codesamu/MISS/3D/animation-scene/bin-sorting.png

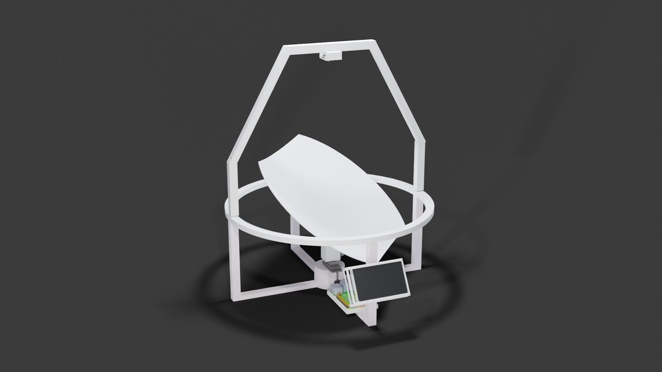
3D/animation-scene/bin-sorting.png
