codesamu/MISS/3D/animation-scene/bin.png

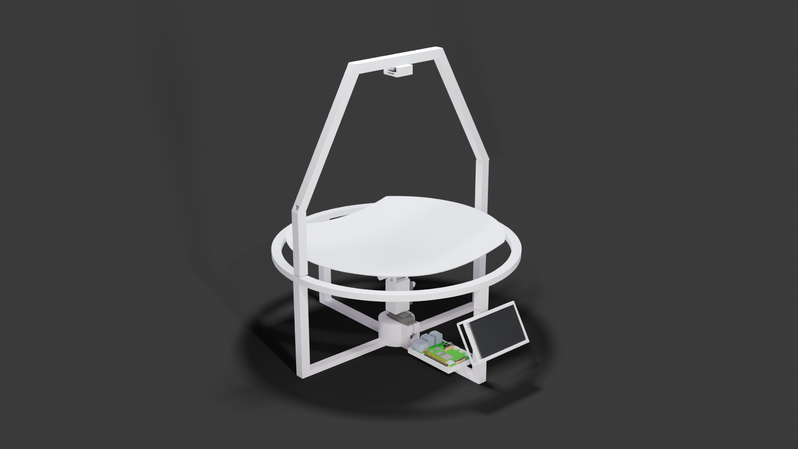
3D/animation-scene/bin.png
