codesamu/MISS/3D/plastic-water-bottle/textures/4715.jpeg

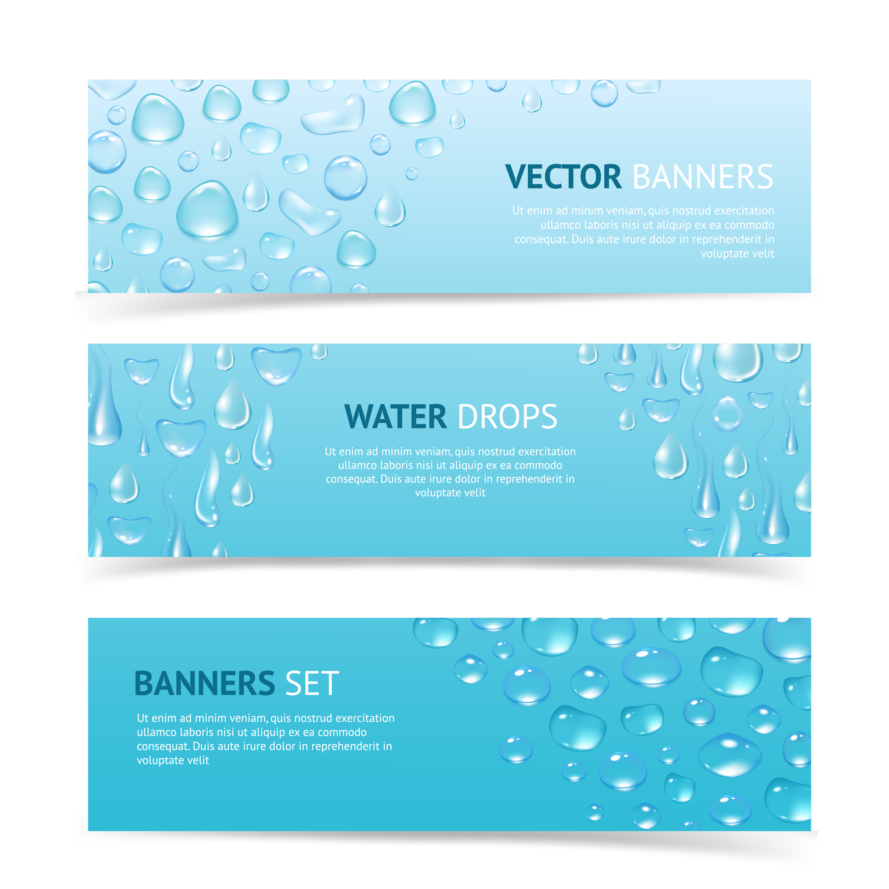
3D/plastic-water-bottle/textures/4715.jpeg
