codesamu/MISS/display-cam-gui/temp_captured.jpg

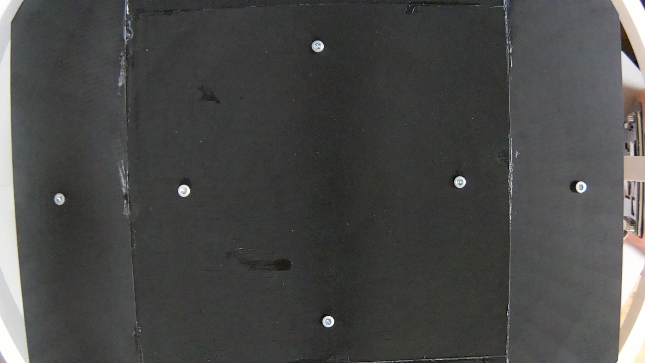
display-cam-gui/temp_captured.jpg
