codesamu/MISS/Doku-IMG/Ablauf-MISS.png

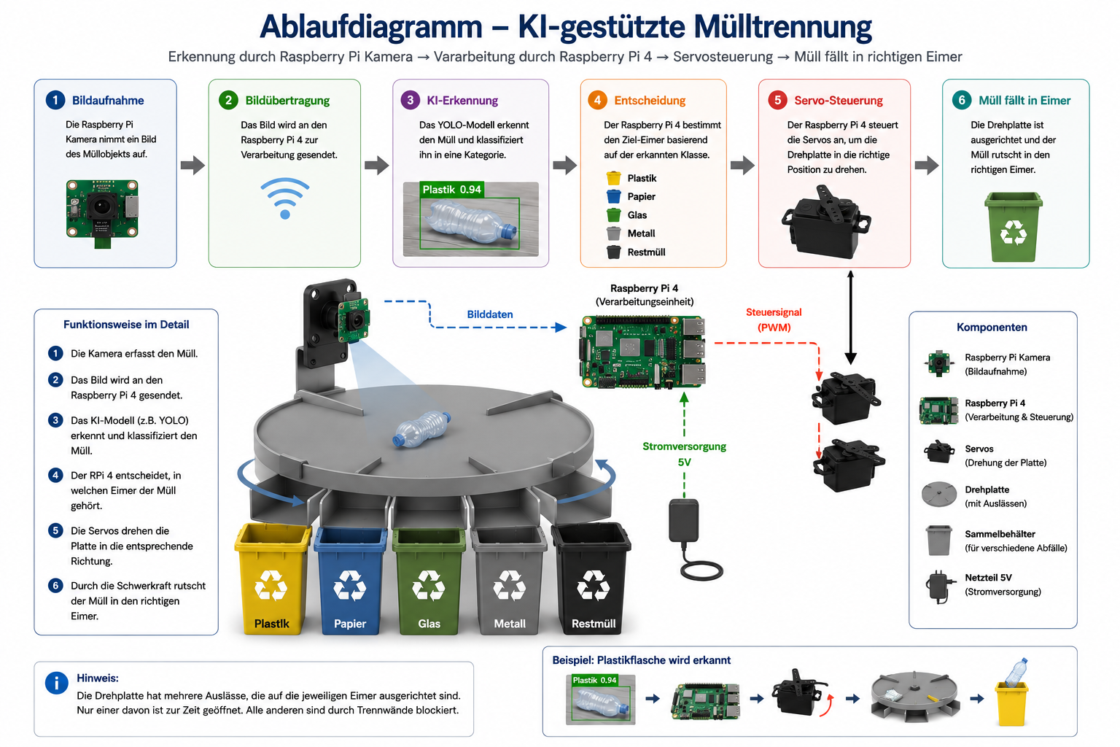
Doku-IMG/Ablauf-MISS.png
