codesamu/MISS/Doku-IMG/AT-Recycle.png

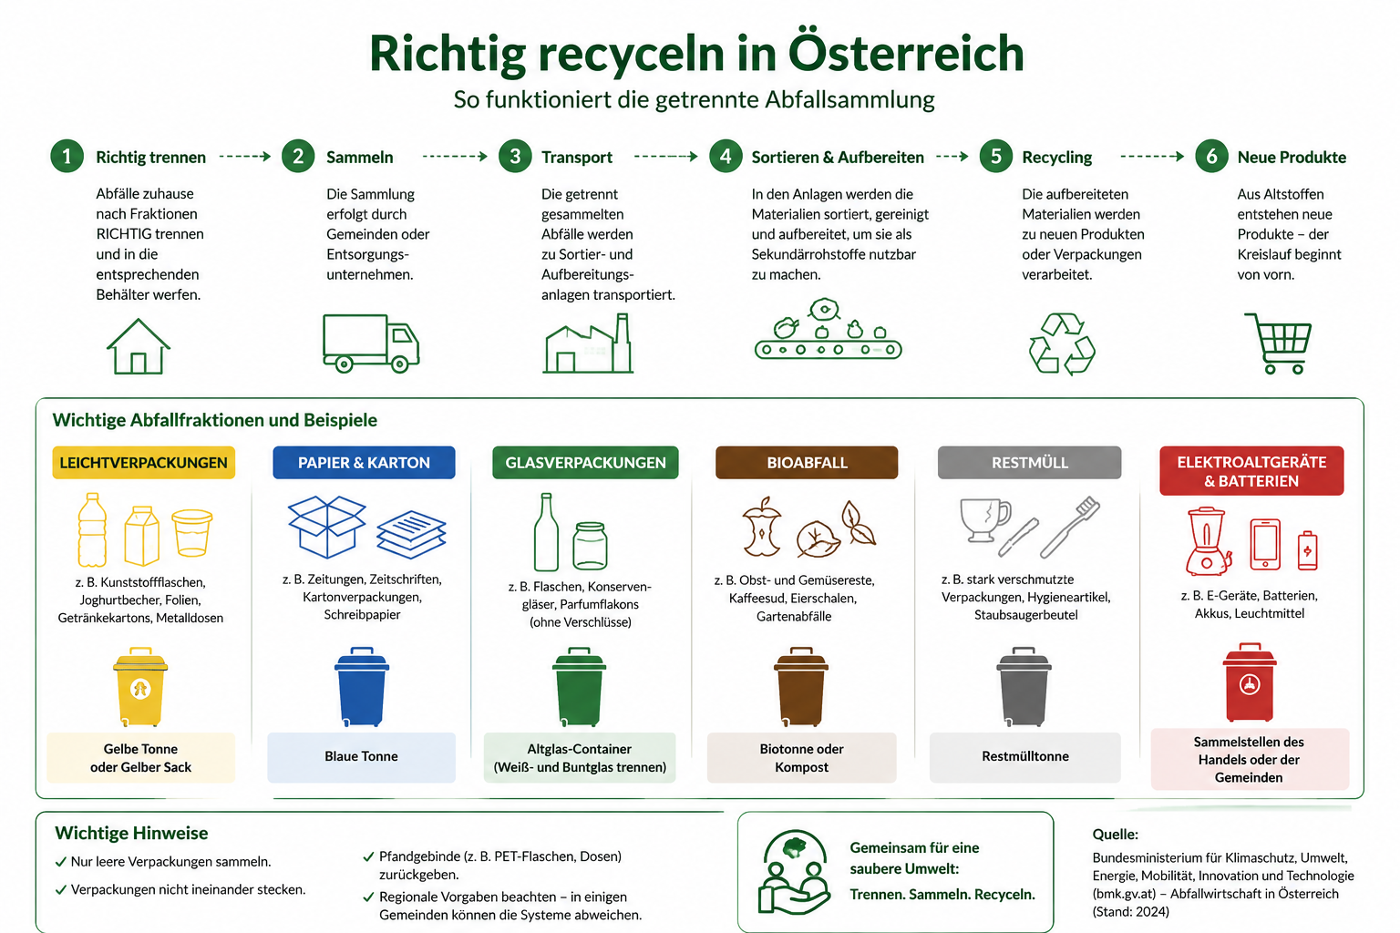
Doku-IMG/AT-Recycle.png
