codesamu/MISS/Doku-IMG/Cam_IMG.png

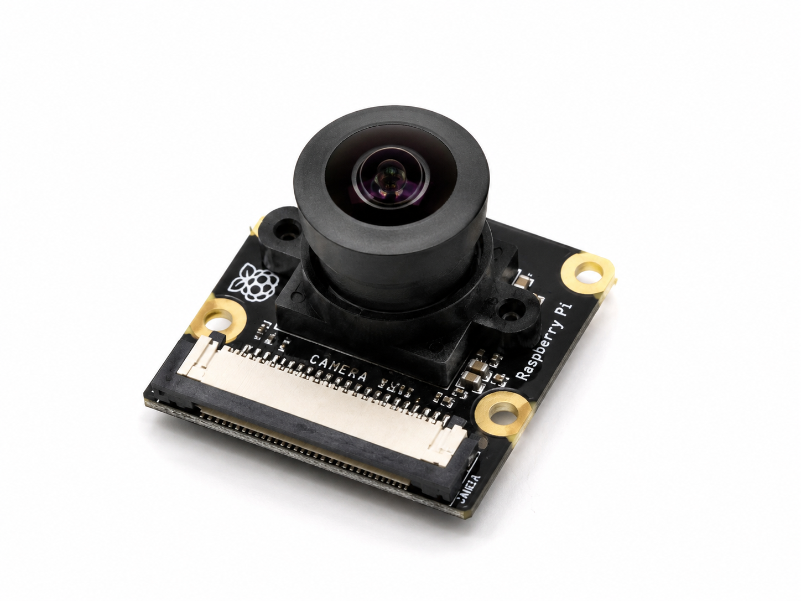
Doku-IMG/Cam_IMG.png
