codesamu/MISS/Doku-IMG/Funktion-YOLO.png

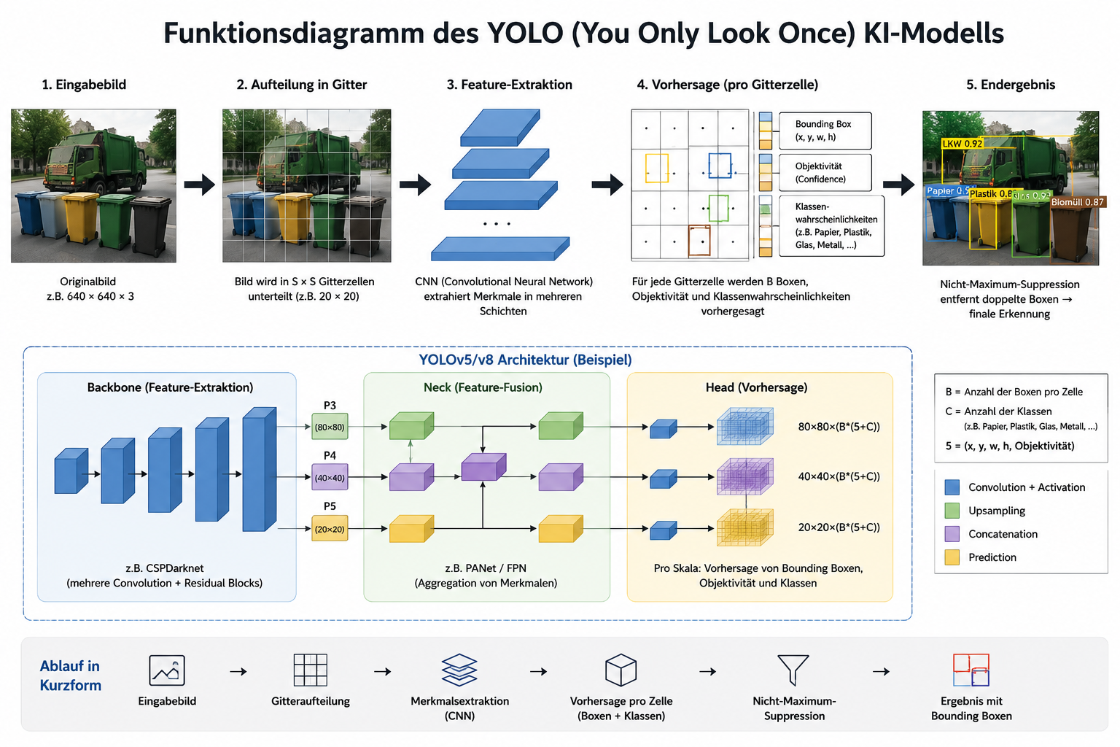
Doku-IMG/Funktion-YOLO.png
