codesamu/MISS/Doku-IMG/Nachhaltigkeit-Trennen.png

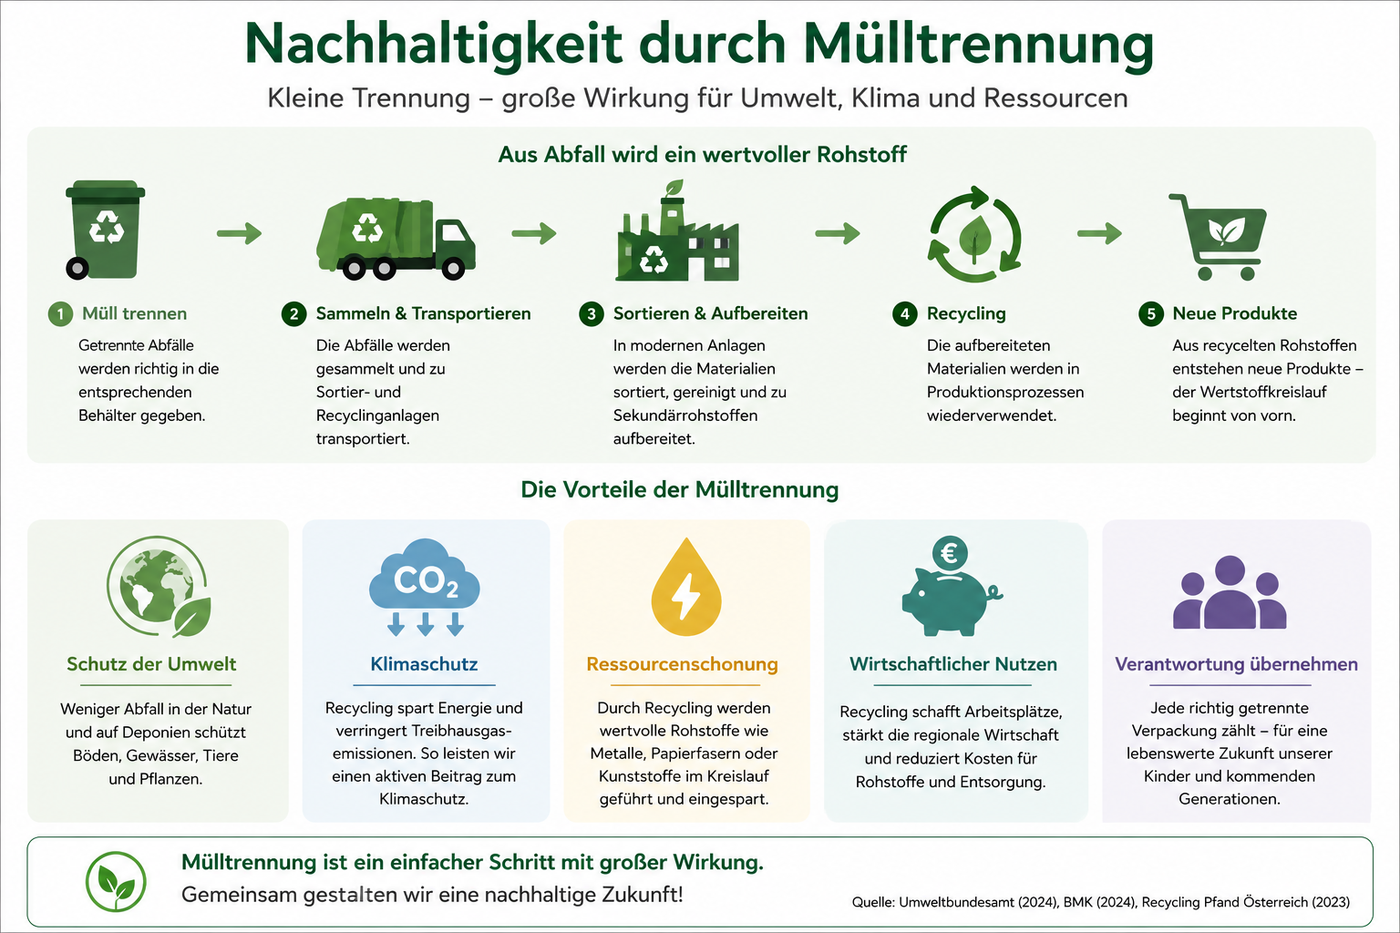
Doku-IMG/Nachhaltigkeit-Trennen.png
