codesamu/MISS/Doku-IMG/RPI_IMG.png

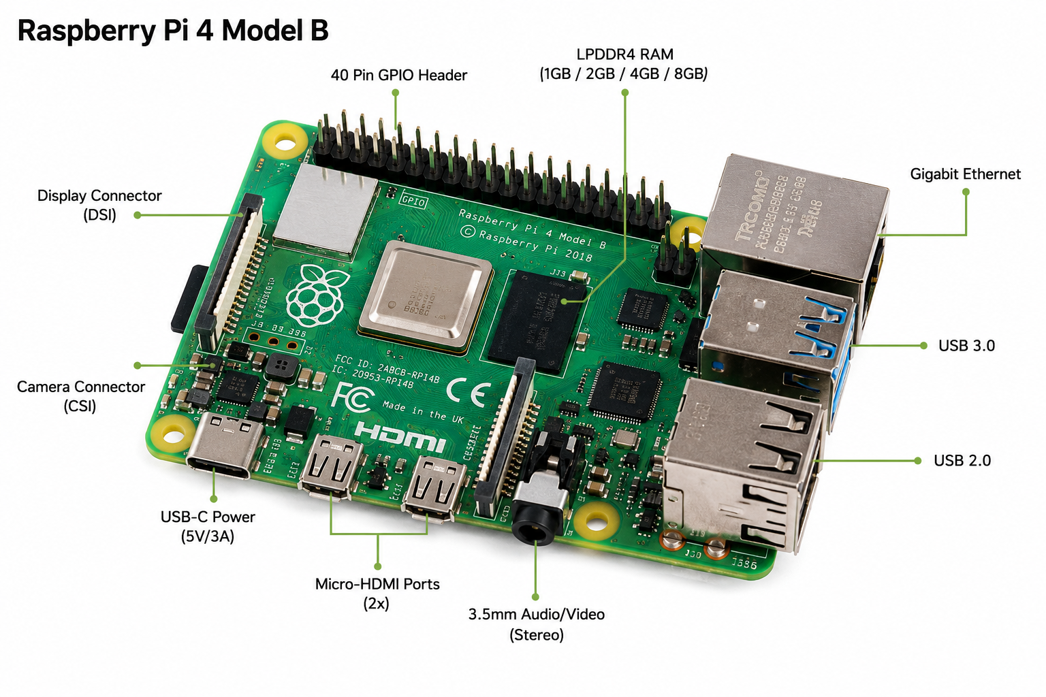
Doku-IMG/RPI_IMG.png
