codesamu/MISS/Doku-IMG/Servo_IMG.png

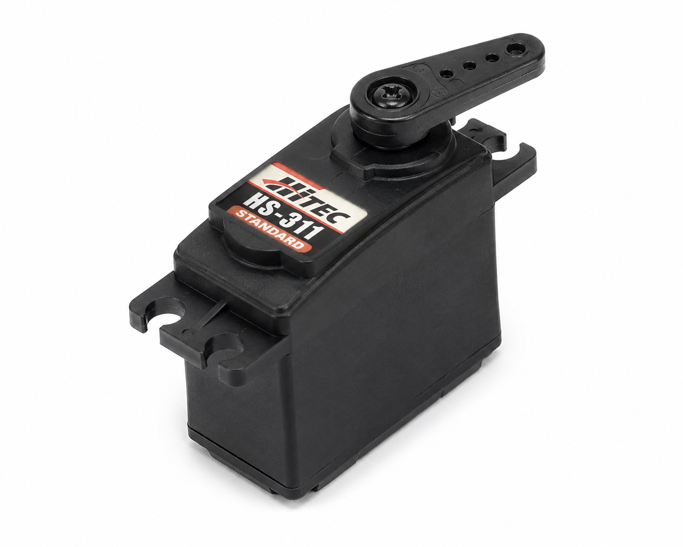
Doku-IMG/Servo_IMG.png
