codesamu/MISS/Doku-IMG/System-Markt.png

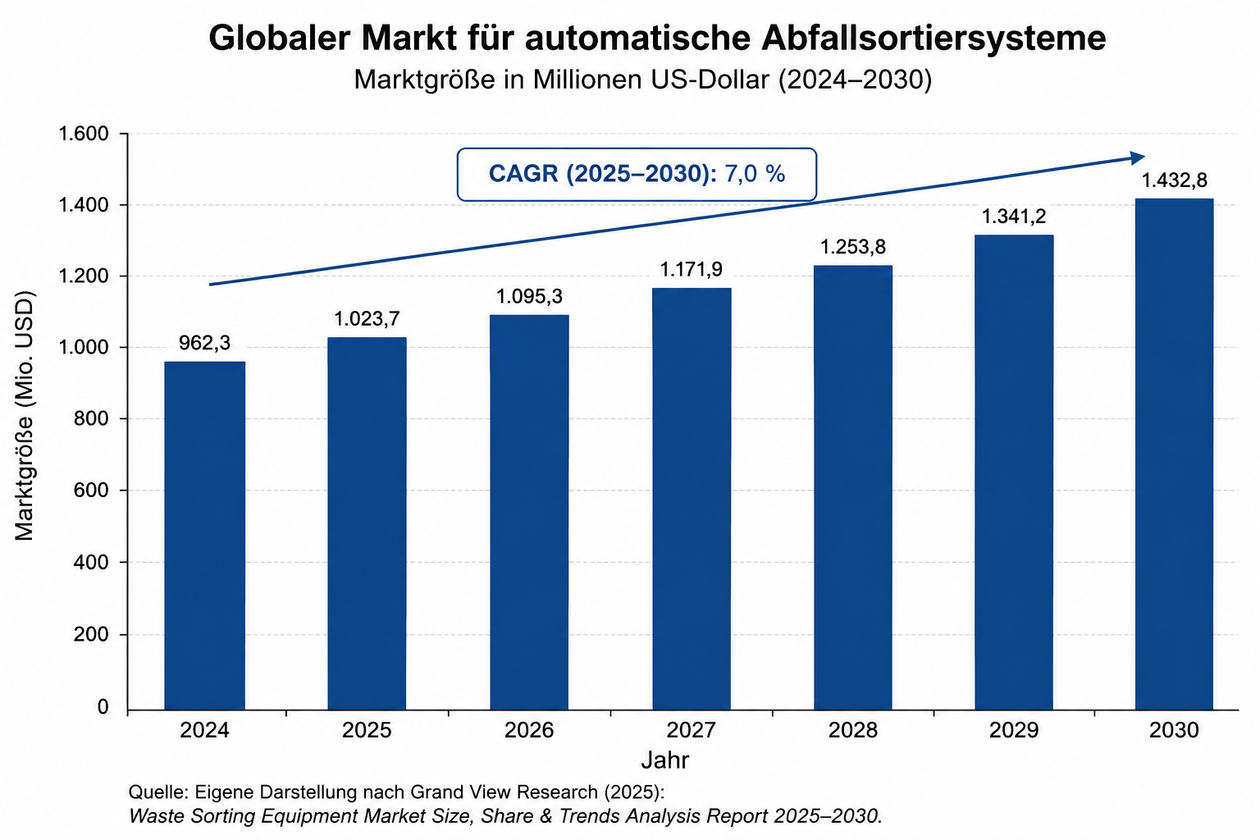
Doku-IMG/System-Markt.png
