codesamu/MISS/YOLO/runs/pet_jhp02naa/train/BoxF1_curve.png

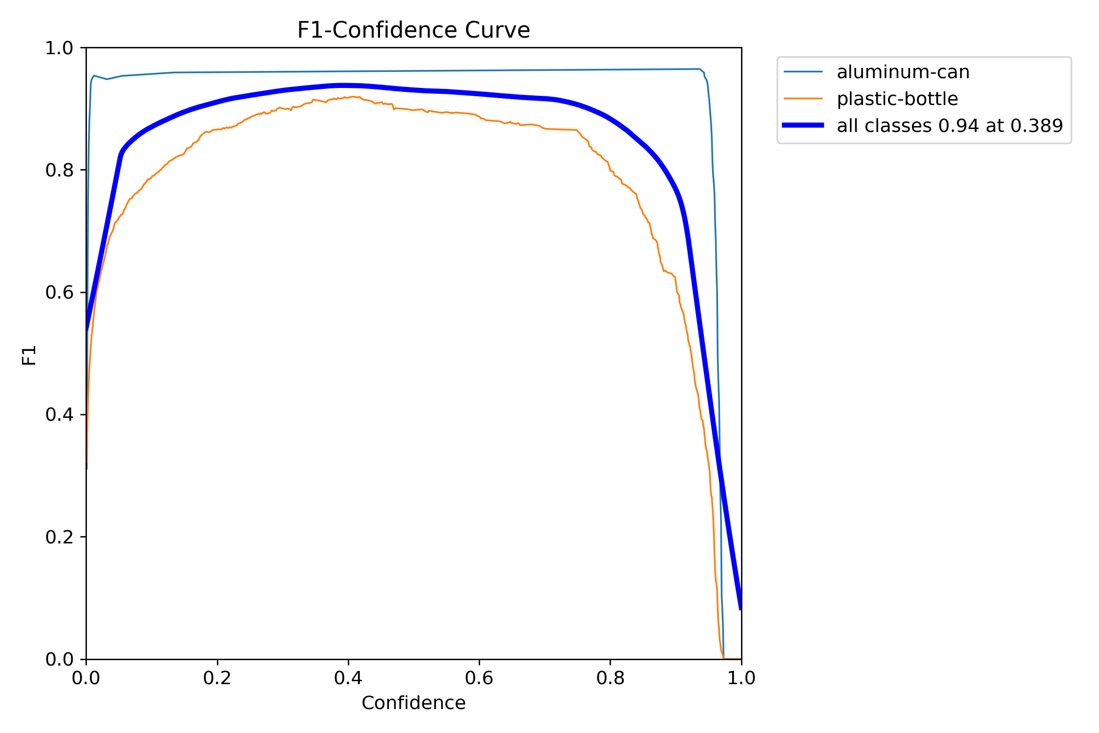
YOLO/runs/pet_jhp02naa/train/BoxF1_curve.png
