codesamu/MISS/YOLO/runs/pet_jhp02naa/train/BoxP_curve.png

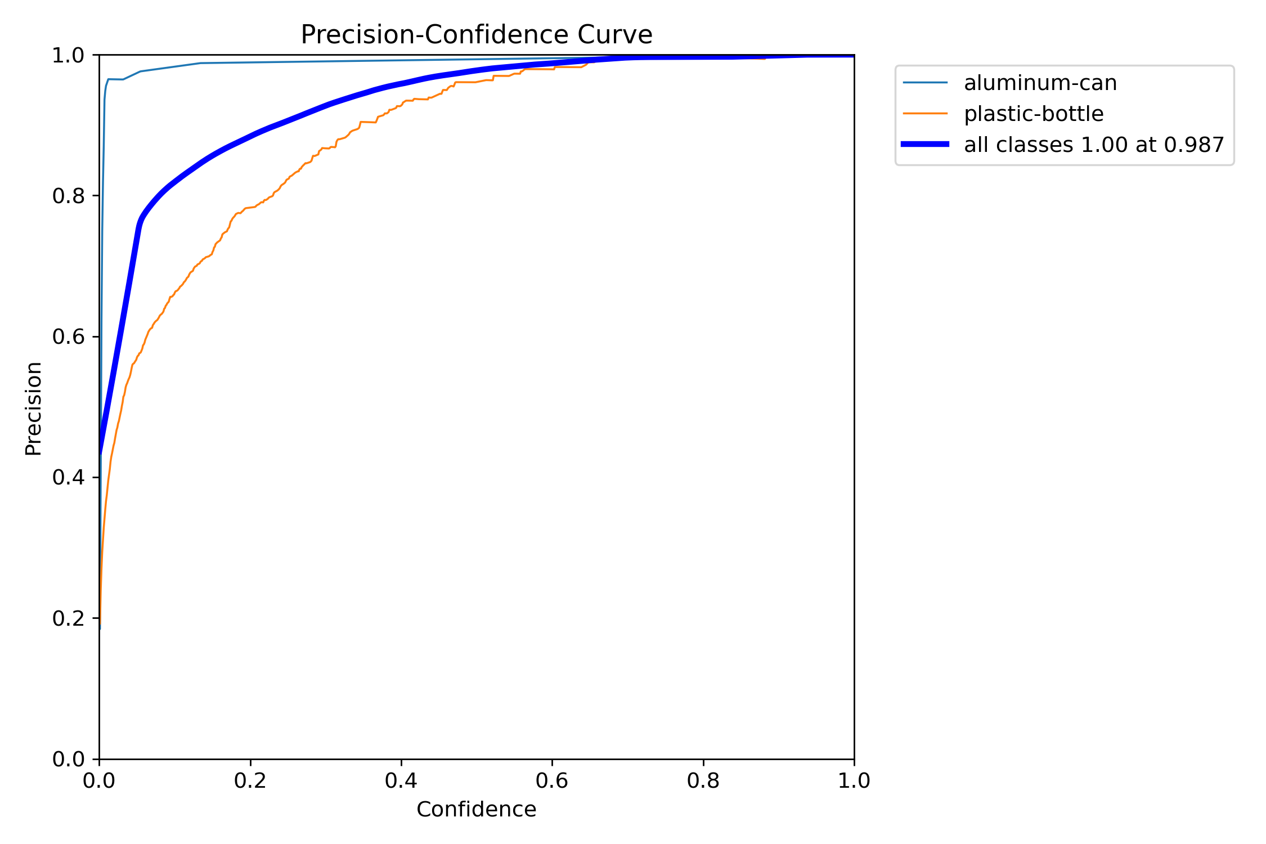
YOLO/runs/pet_jhp02naa/train/BoxP_curve.png
