codesamu/MISS/YOLO/runs/pet_jhp02naa/train/BoxPR_curve.png

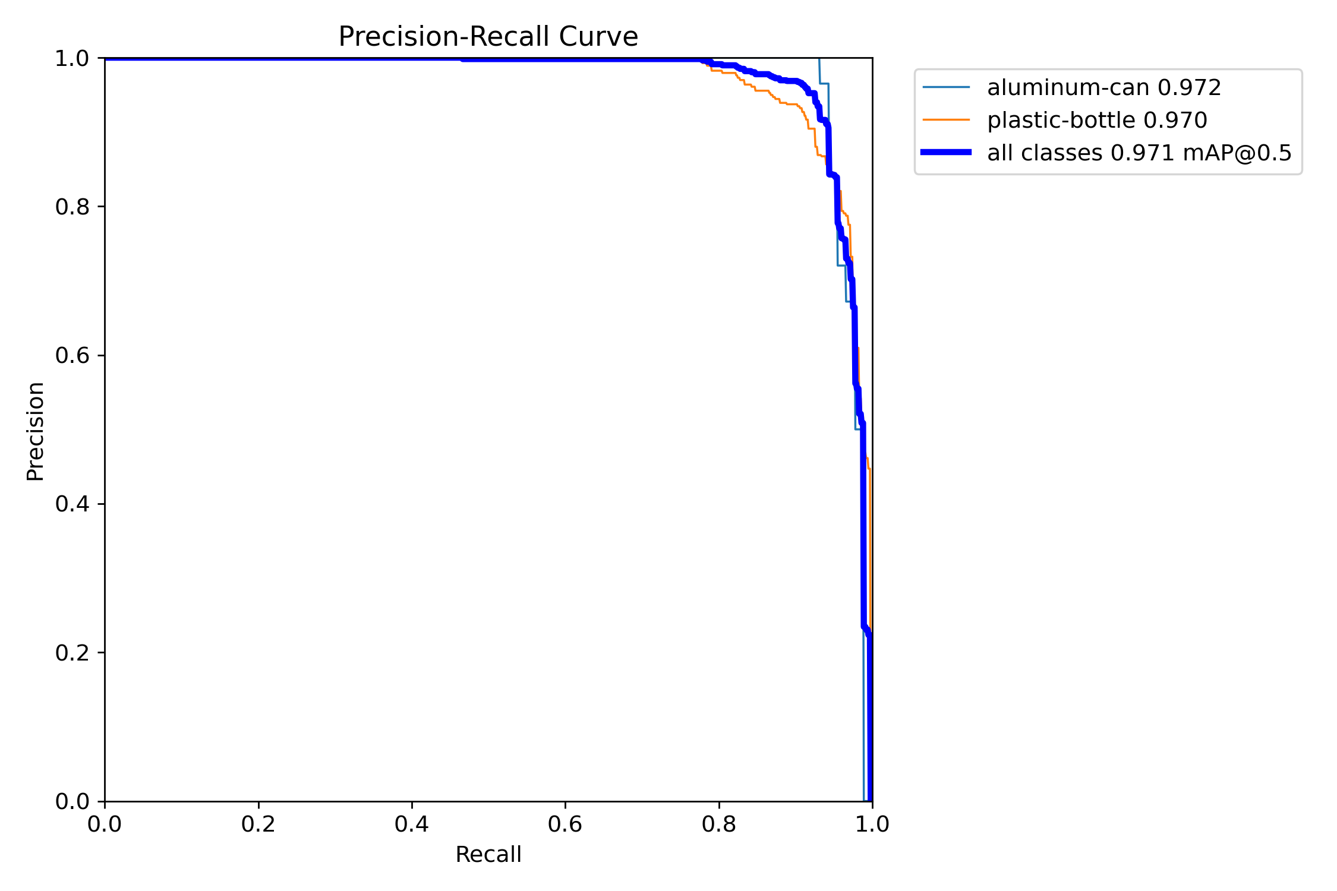
YOLO/runs/pet_jhp02naa/train/BoxPR_curve.png
