codesamu/MISS/YOLO/runs/pet_jhp02naa/train/BoxR_curve.png

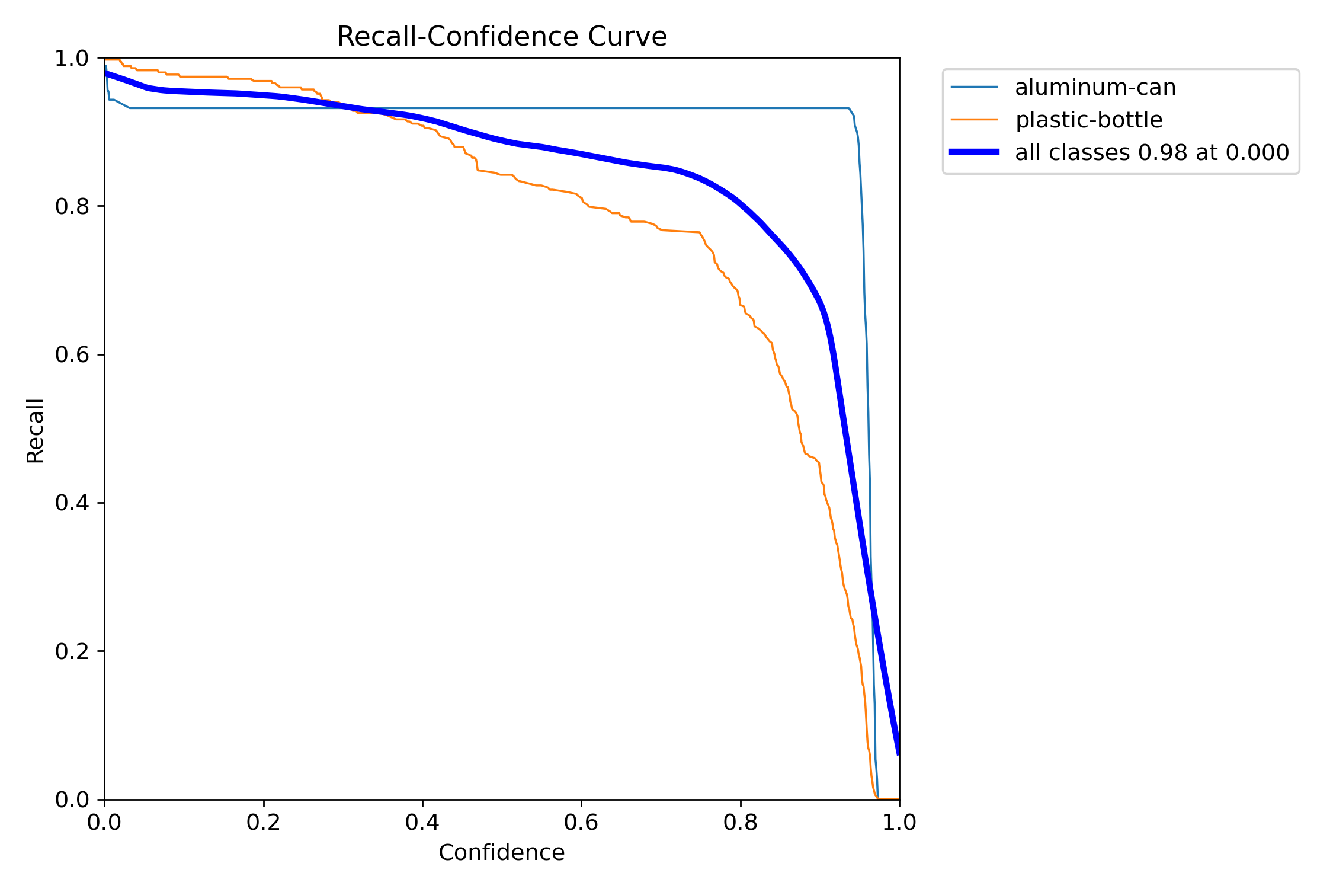
YOLO/runs/pet_jhp02naa/train/BoxR_curve.png
