codesamu/MISS/YOLO/runs/pet_jhp02naa/train/confusion_matrix.png

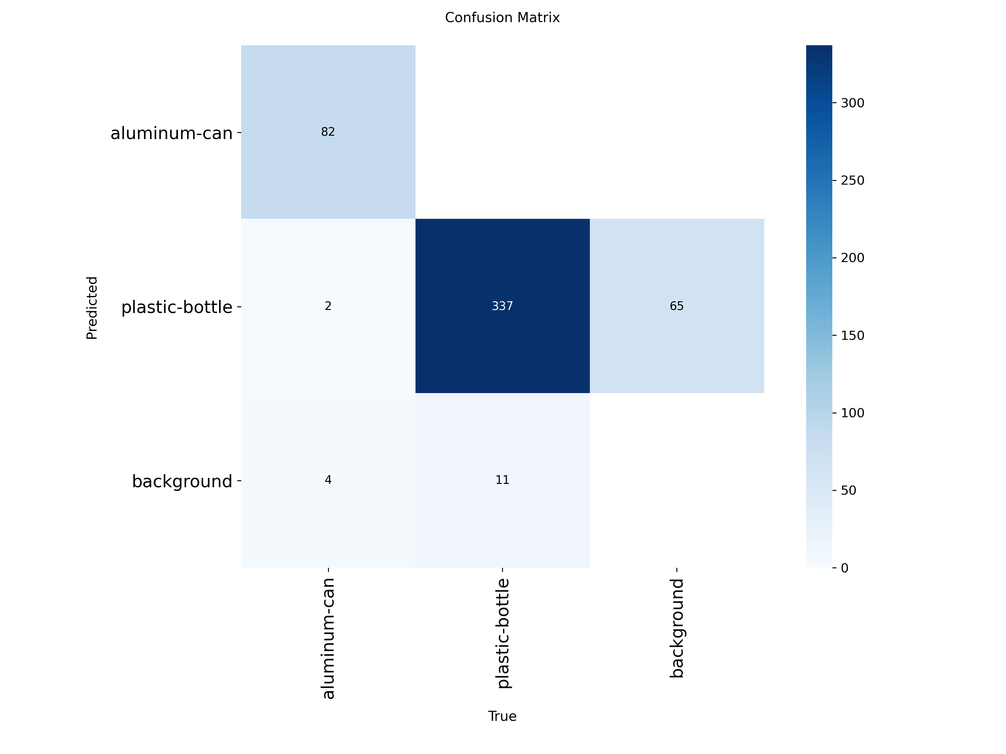
YOLO/runs/pet_jhp02naa/train/confusion_matrix.png
