codesamu/MISS/YOLO/runs/pet_jhp02naa/train/confusion_matrix_normalized.png

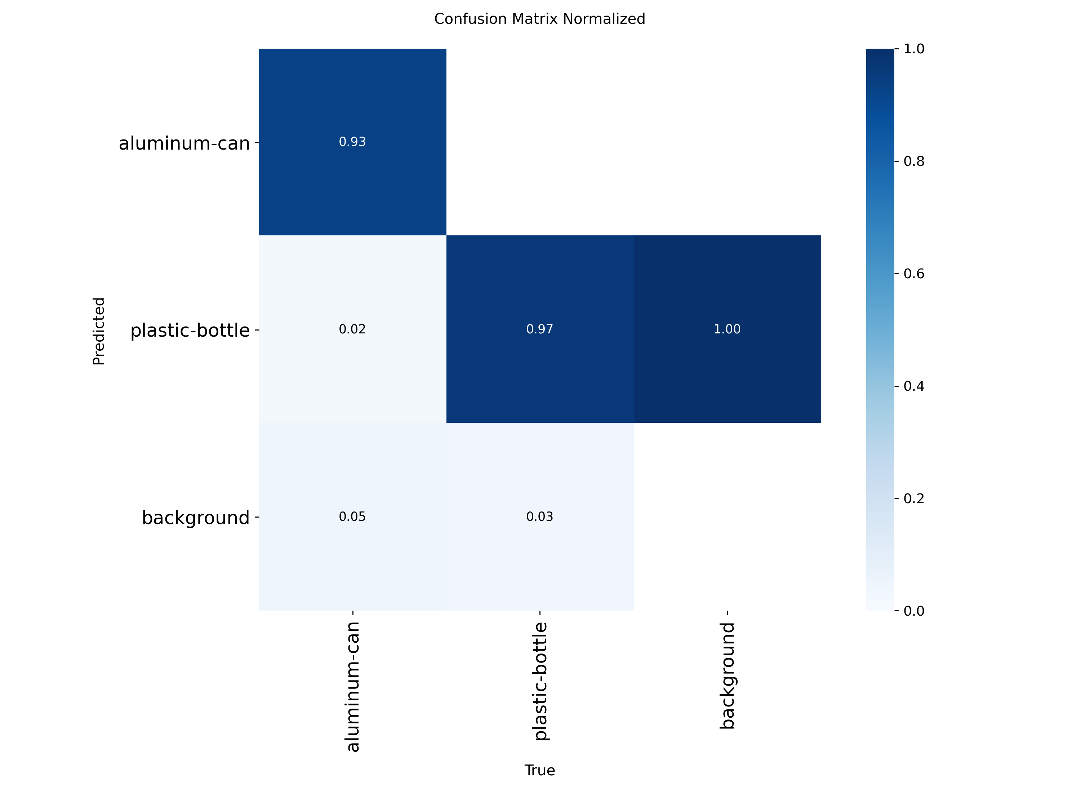
YOLO/runs/pet_jhp02naa/train/confusion_matrix_normalized.png
