codesamu/MISS/YOLO/runs/pet_jhp02naa/train/labels.jpg

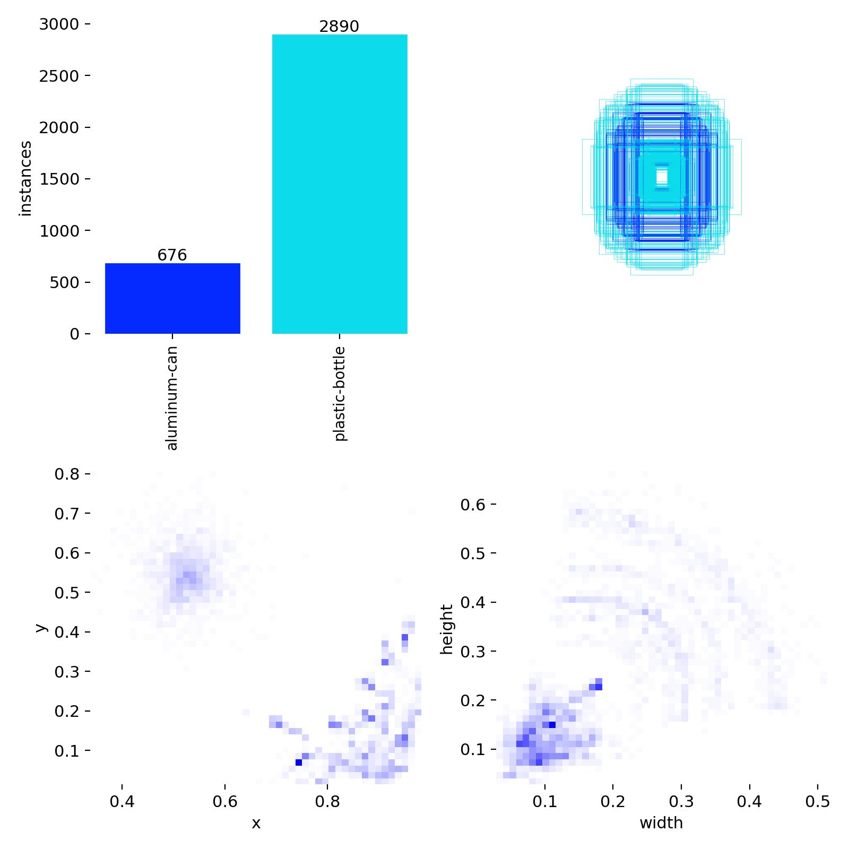
YOLO/runs/pet_jhp02naa/train/labels.jpg
