codesamu/MISS/YOLO/runs/pet_jhp02naa/train/train_batch1.jpg

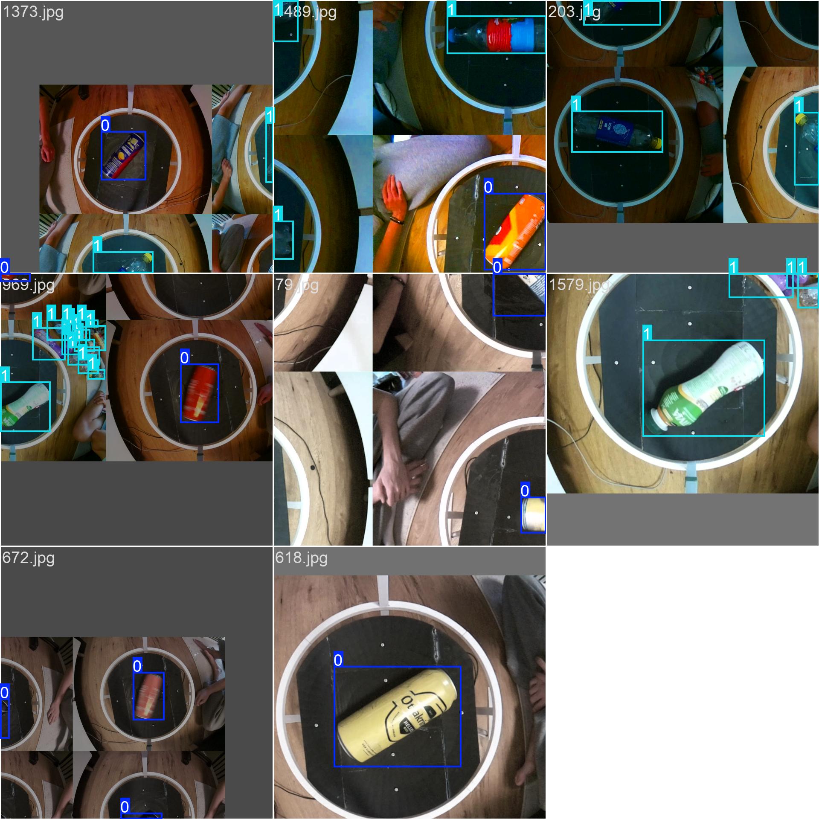
YOLO/runs/pet_jhp02naa/train/train_batch1.jpg
