codesamu/MISS/YOLO/runs/pet_jhp02naa/train/train_batch3480.jpg

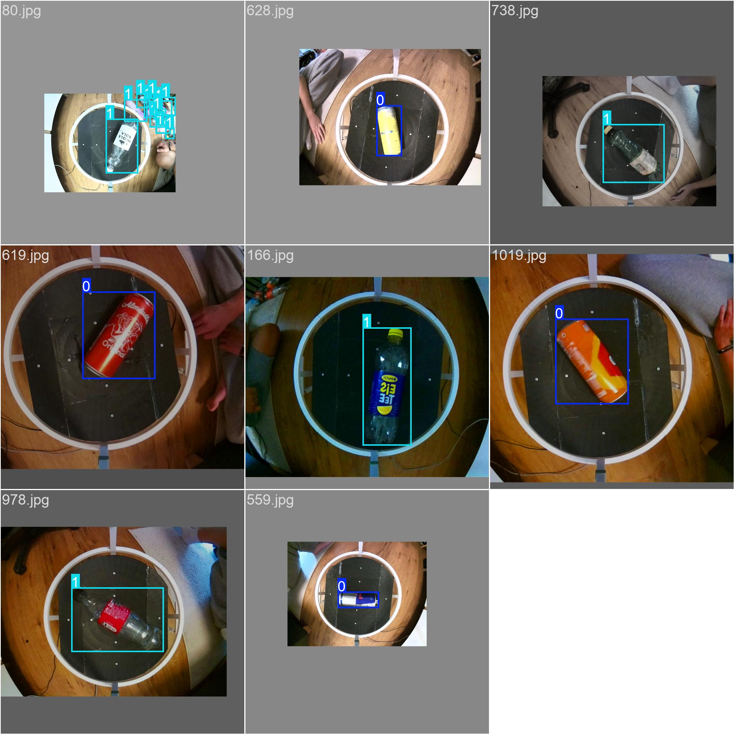
YOLO/runs/pet_jhp02naa/train/train_batch3480.jpg
