codesamu/MISS/YOLO/runs/pet_jhp02naa/train/train_batch3481.jpg

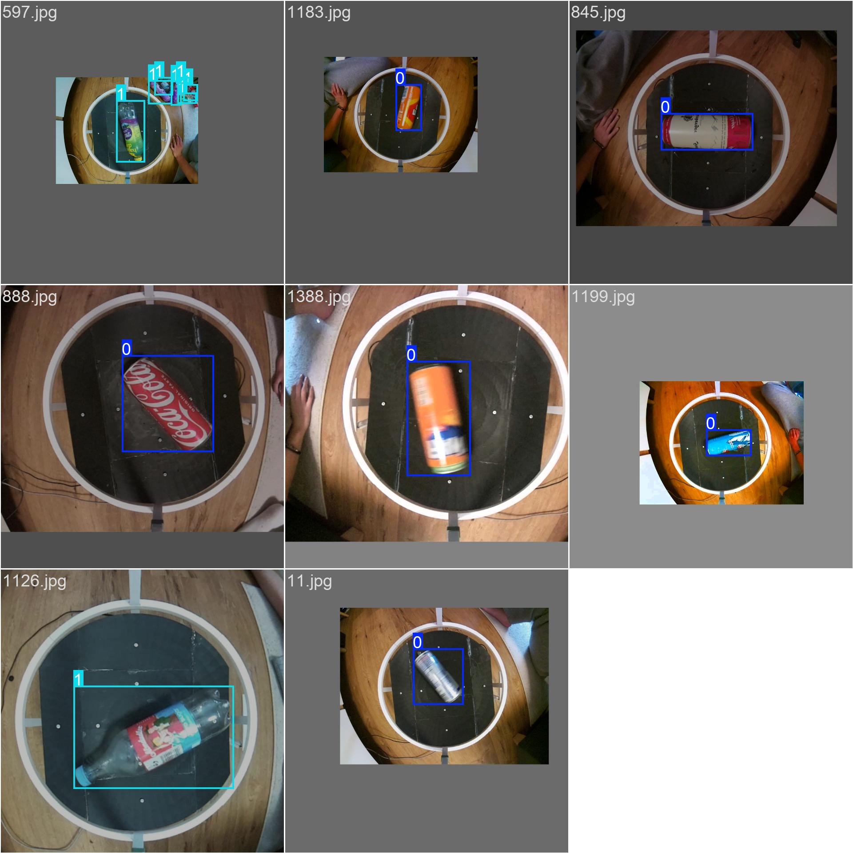
YOLO/runs/pet_jhp02naa/train/train_batch3481.jpg
