codesamu/MISS/YOLO/runs/pet_jhp02naa/train/val_batch2_labels.jpg

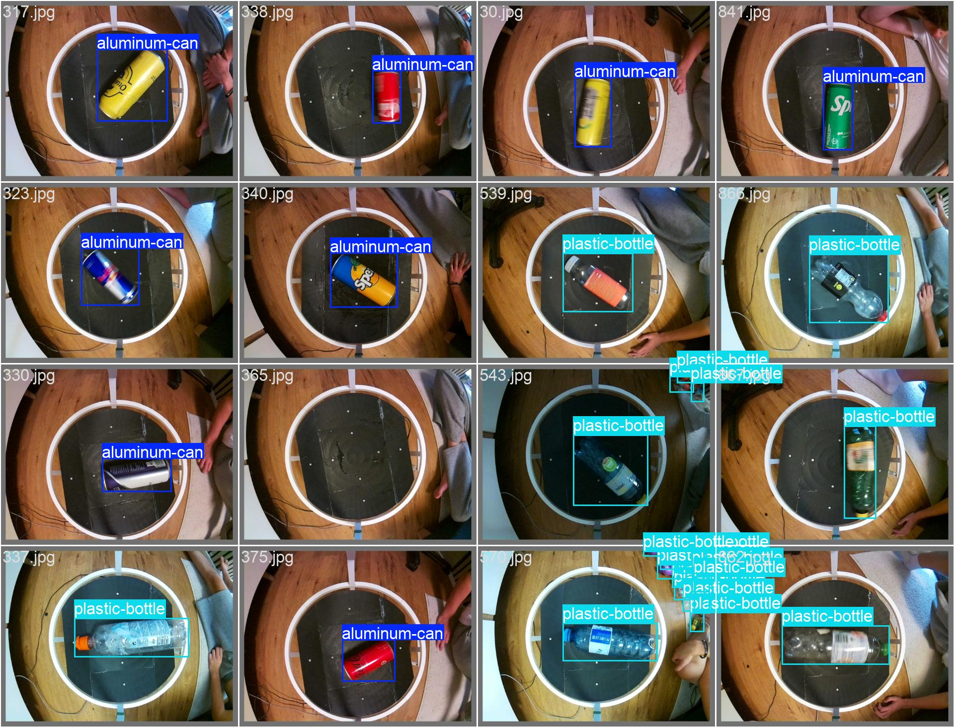
YOLO/runs/pet_jhp02naa/train/val_batch2_labels.jpg
