codesamu/MISS/YOLO/runs/pet_s0xe5pm9/train/train_batch1501.jpg

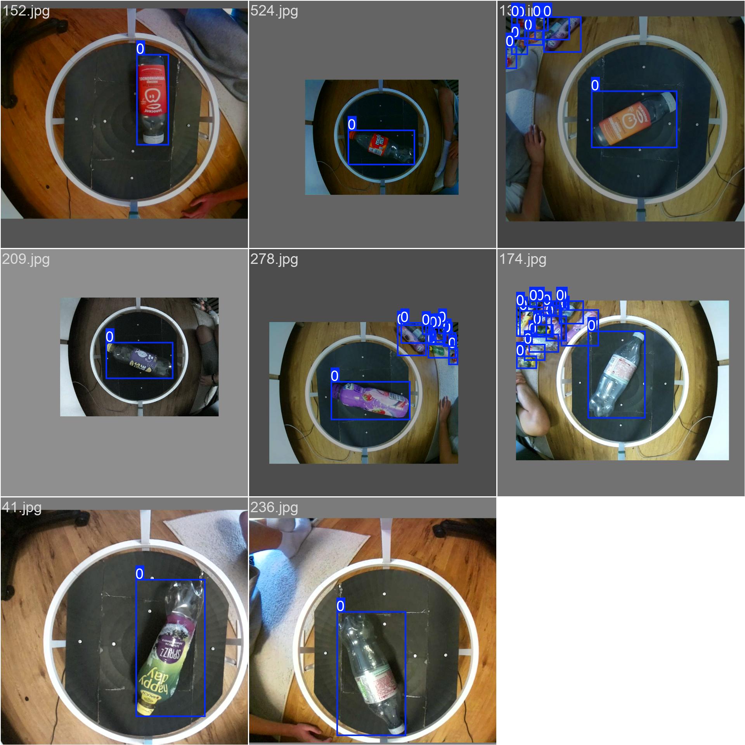
YOLO/runs/pet_s0xe5pm9/train/train_batch1501.jpg
