codesamu/MISS/YOLO/runs/pet_s0xe5pm9/train/train_batch1502.jpg

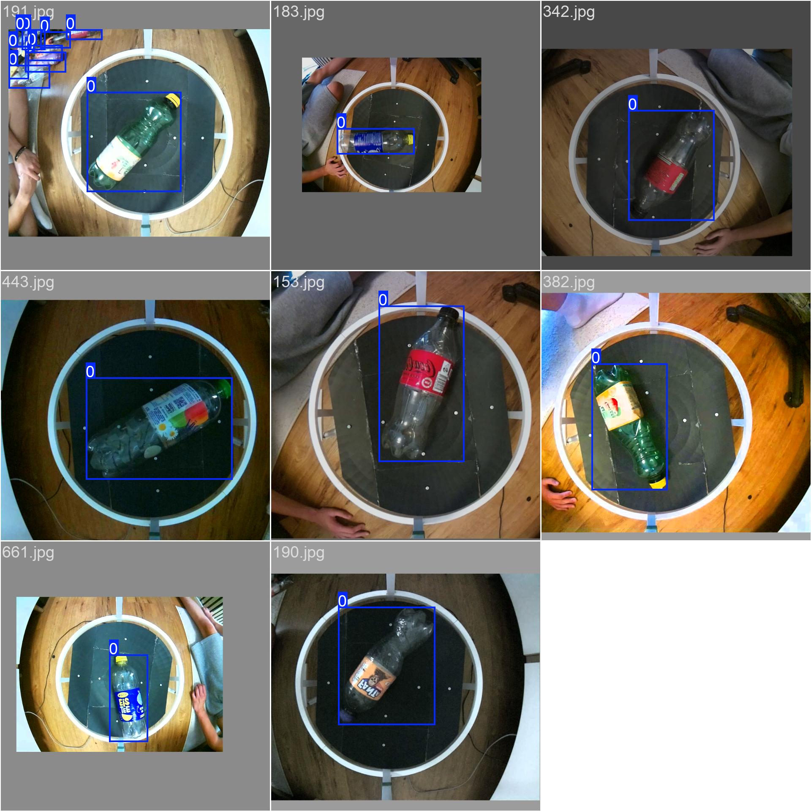
YOLO/runs/pet_s0xe5pm9/train/train_batch1502.jpg
