codesamu/MISS/3D/bin-base-multipart.FCStd

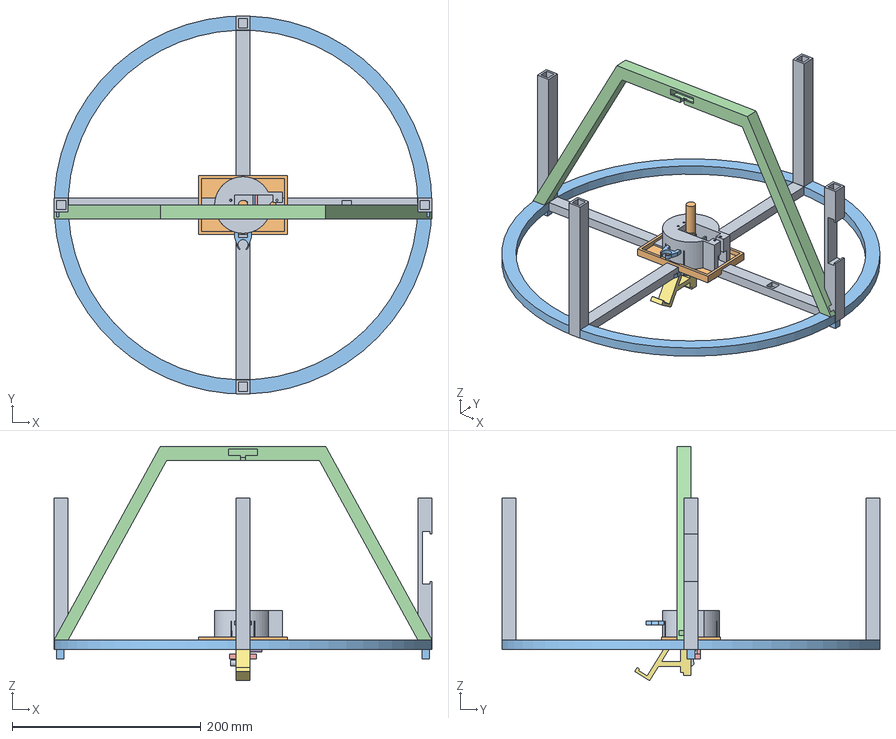
[picture p47: CAD file, 2026-06-30]
3D/bin-base-multipart.FCStd
400.0 x 400.0 x 248.1 mm
base
rpi-mount
ring
camera-rig
camera-mount
Plate conn-lock
display-mnt
Servo-pushrod
Middle-pushrod
End-pushrod
servo-on-servo
lock-pushrod
pushrod-plate-locker
