codesamu/MISS/3D/Pi Camera Module v3 Wide Angle.STL

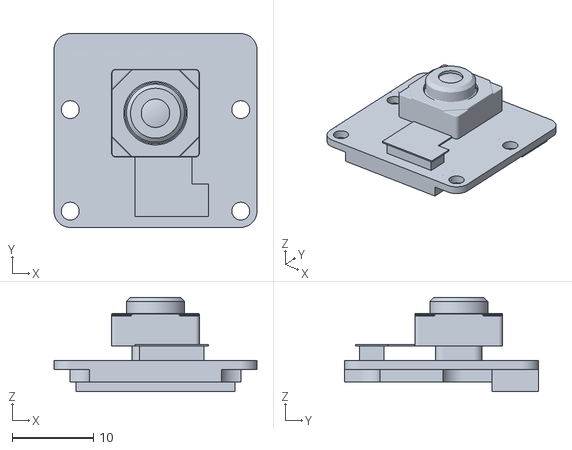
[picture p48: CAD file, 2026-06-30]
3D/Pi Camera Module v3 Wide Angle.STL
25.0 x 23.9 x 11.6
