codesamu/MISS/3D/bin-pushrod-plate-locker.3mf

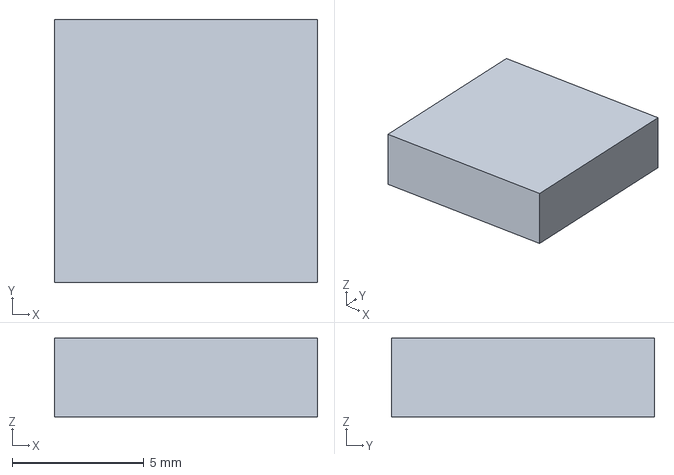
[picture p49: CAD file, 2026-05-06]
3D/bin-pushrod-plate-locker.3mf
10.0 x 10.0 x 3.00 mm
