codesamu/MISS/3D/bin-middle-pushrod.3mf

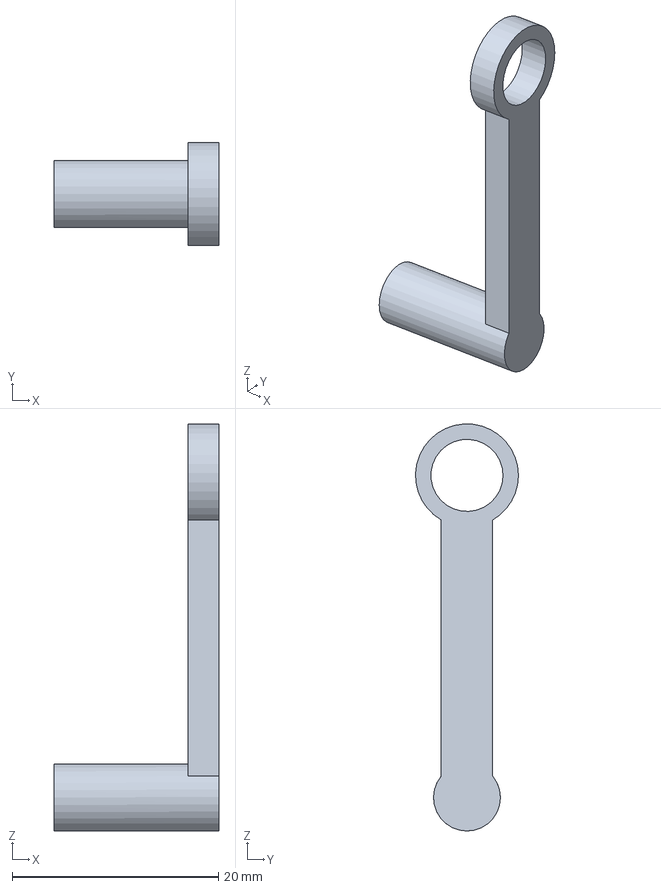
[picture p50: CAD file, 2026-05-06]
3D/bin-middle-pushrod.3mf
16.0 x 9.99 x 39.5 mm
