codesamu/MISS/3D/bin-lock-pushrod.3mf

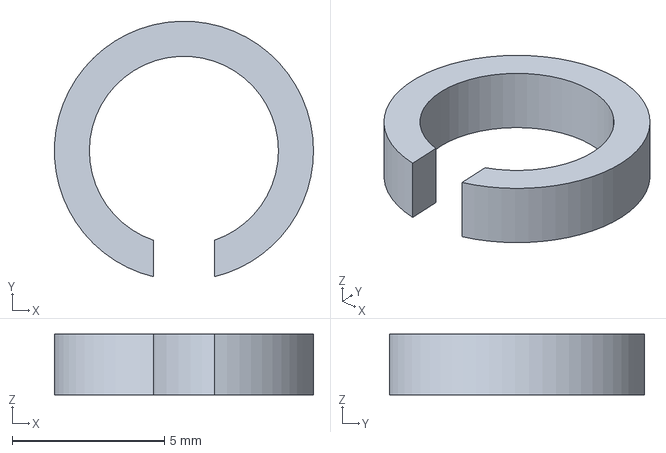
[picture p51: CAD file, 2026-05-06]
3D/bin-lock-pushrod.3mf
8.49 x 8.38 x 2.00 mm
