codesamu/MISS/Doku-IMG/Aufbau.jpg

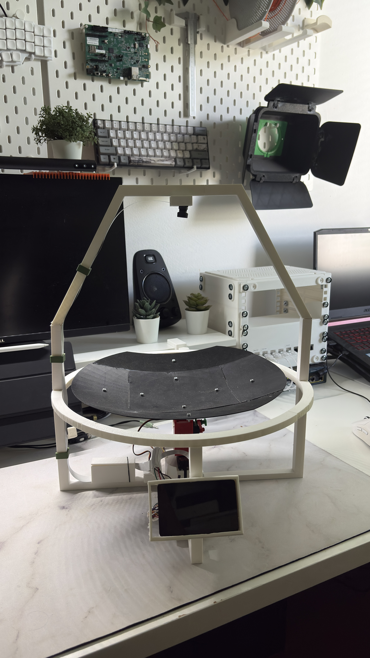
Doku-IMG/Aufbau.jpg
