codesamu/MISS/YOLO/runs/pet_jhp02naa/test/val_batch0_labels.jpg

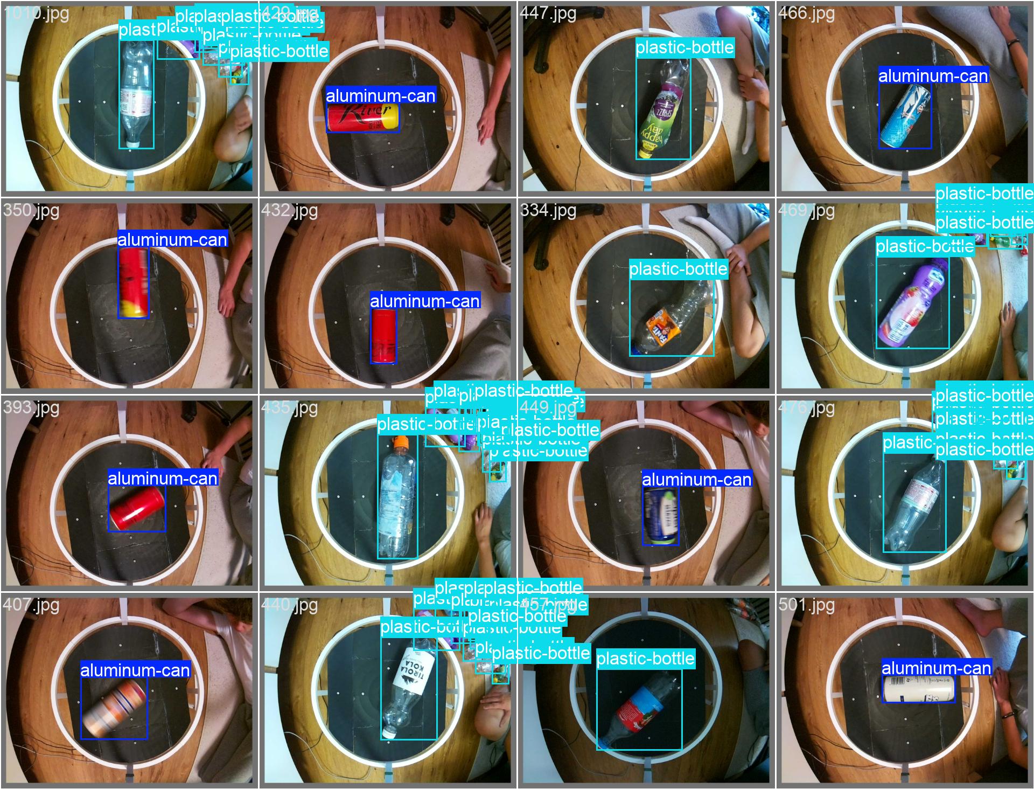
YOLO/runs/pet_jhp02naa/test/val_batch0_labels.jpg
