codesamu/MISS/YOLO/runs/pet_jhp02naa/train/results.png

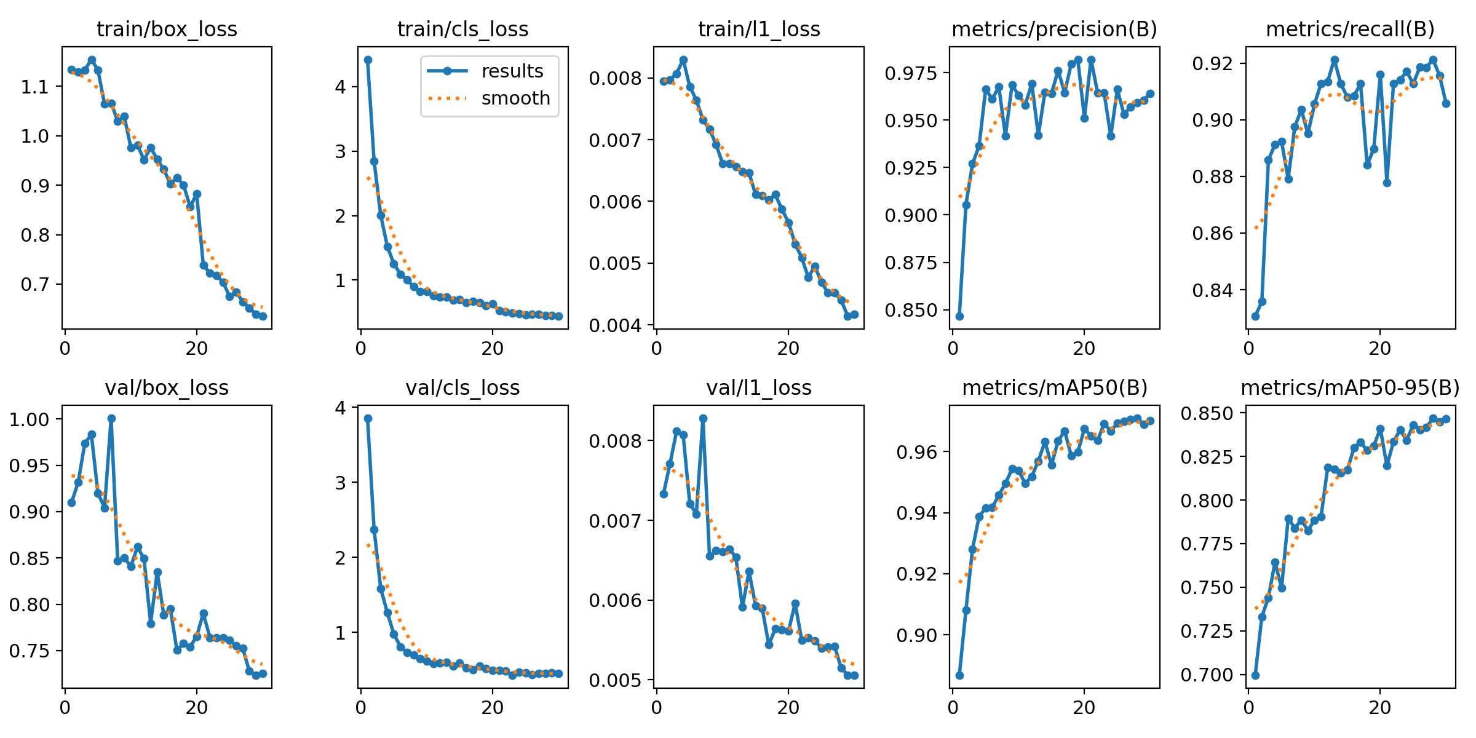
YOLO/runs/pet_jhp02naa/train/results.png
